arrowSoftware/8BitCPU/Images/8-BitRegister.gif

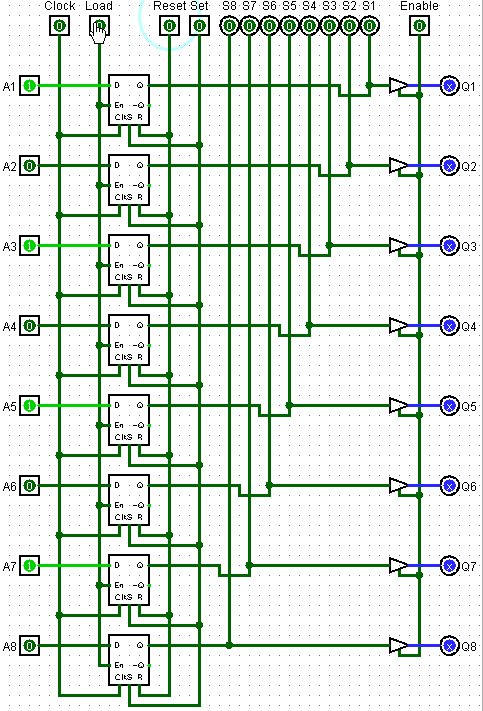
Images/8-BitRegister.gif
