arrowSoftware/8BitCPU/Images/8-BitRegister.png

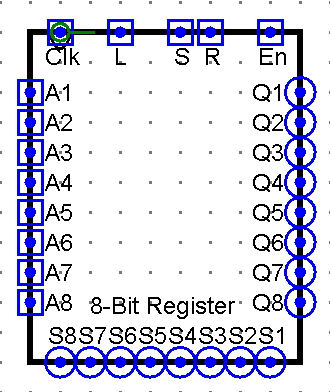
Images/8-BitRegister.png
