arrowSoftware/8BitCPU/Images/AvailableRegisters.png

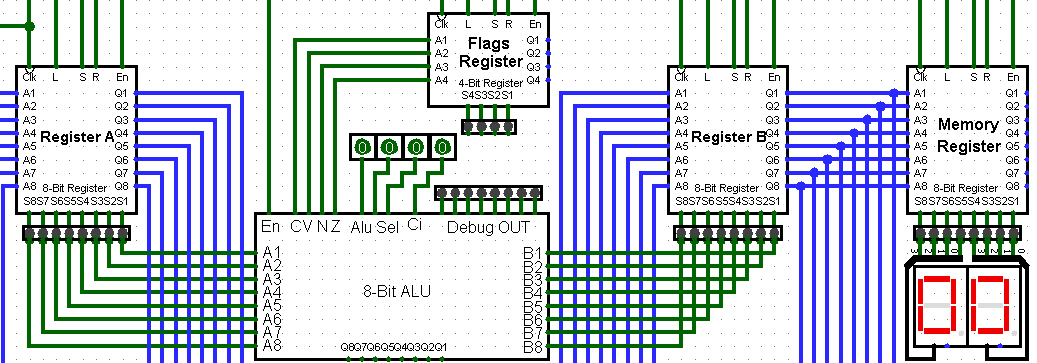
Images/AvailableRegisters.png
