arrowSoftware/8BitCPU/Images/J-KFlipFlop.png

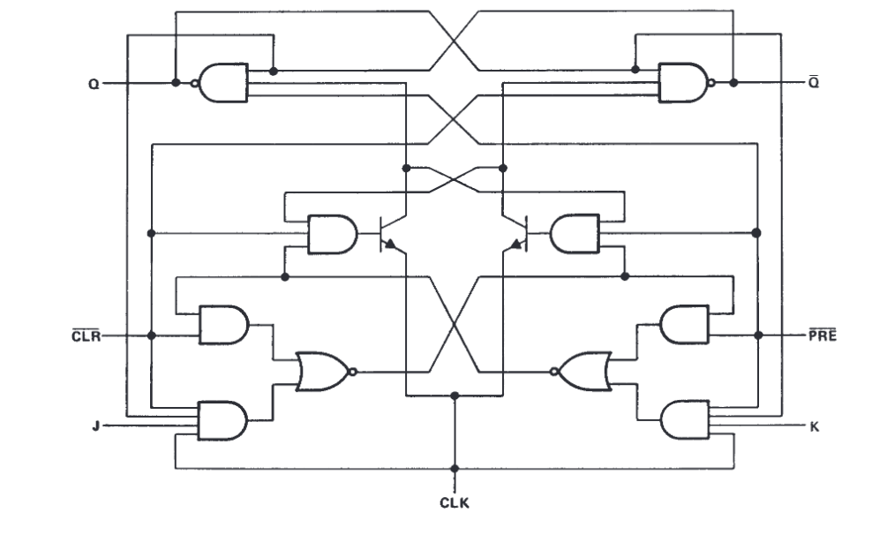
Images/J-KFlipFlop.png
