arrowSoftware/8BitCPU/Images/PCRegister.PNG

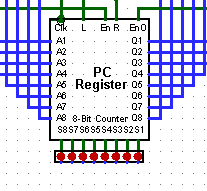
Images/PCRegister.PNG
