arrowSoftware/8BitCPU/Logism/8-Bit Add_Sub.png

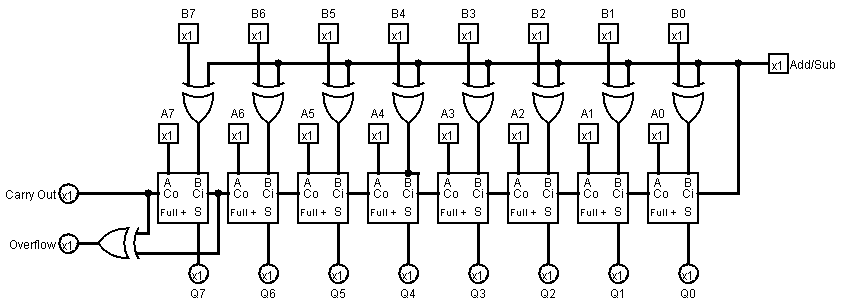
Logism/8-Bit Add_Sub.png
