arrowSoftware/8BitCPU/Logism/8-Bit Adder.png

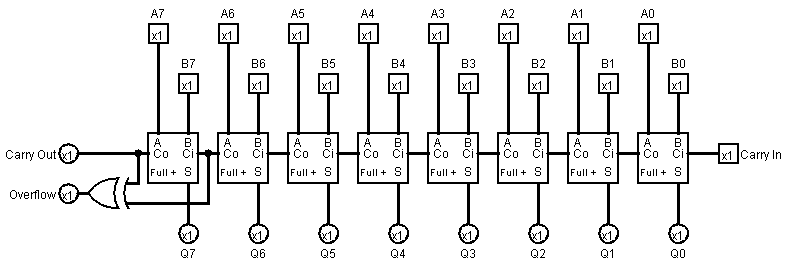
Logism/8-Bit Adder.png
